kinpro1024/ErgoWarrior/Assets/ErgoWarrior_v0_alpha.jpg

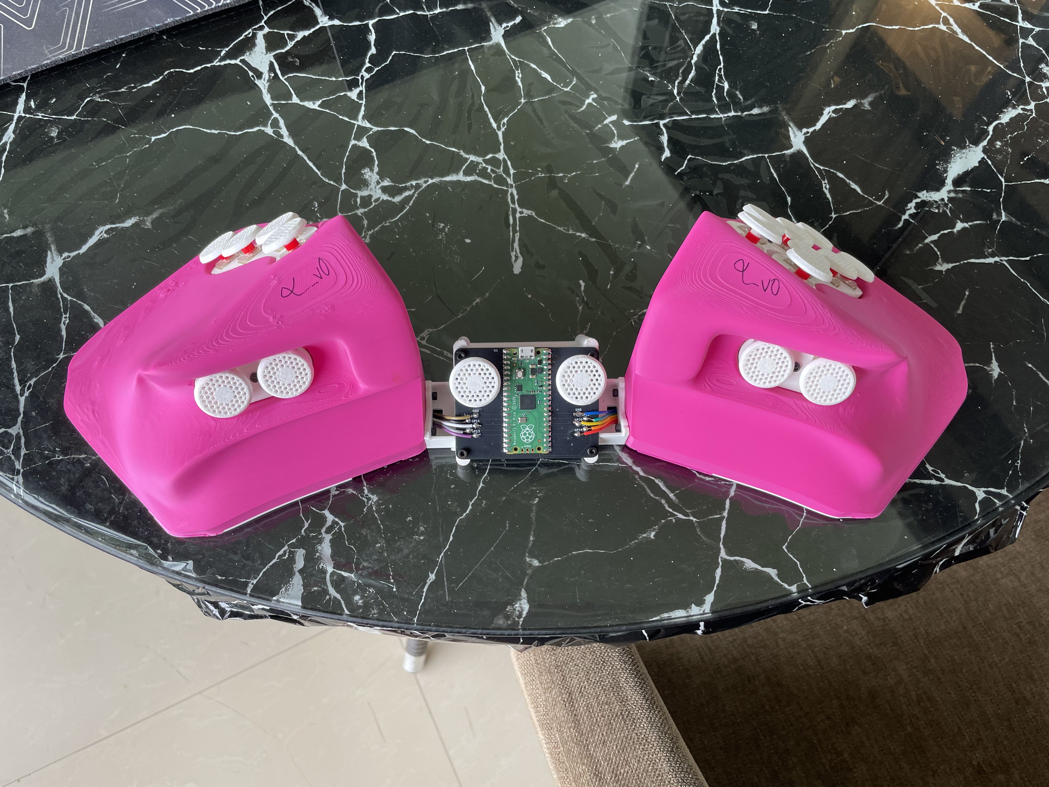
Assets/ErgoWarrior_v0_alpha.jpg
