kinpro1024/ErgoWarrior/Assets/Reference_Images/Screenshot 2025-11-22 at 19.15.04.png

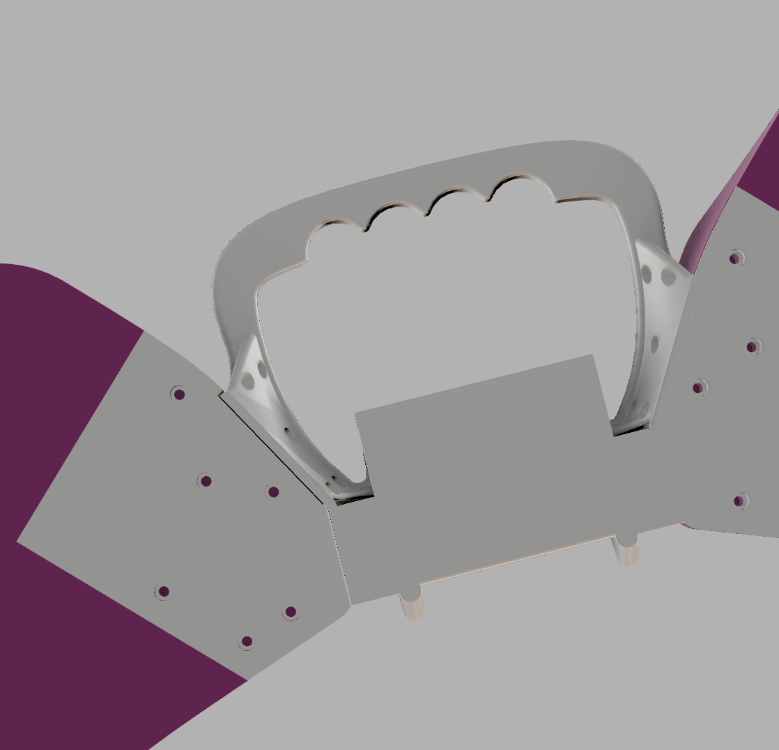
Assets/Reference_Images/Screenshot 2025-11-22 at 19.15.04.png
