kinpro1024/ErgoWarrior/Assets/Reference_Images/Screenshot 2025-11-22 at 19.16.22.png

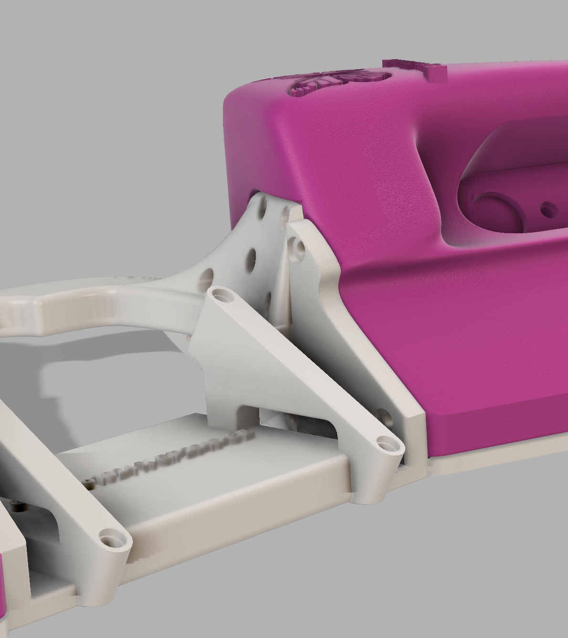
Assets/Reference_Images/Screenshot 2025-11-22 at 19.16.22.png
