kinpro1024/ErgoWarrior/Assets/v0_vs_v1_PCBs.jpg

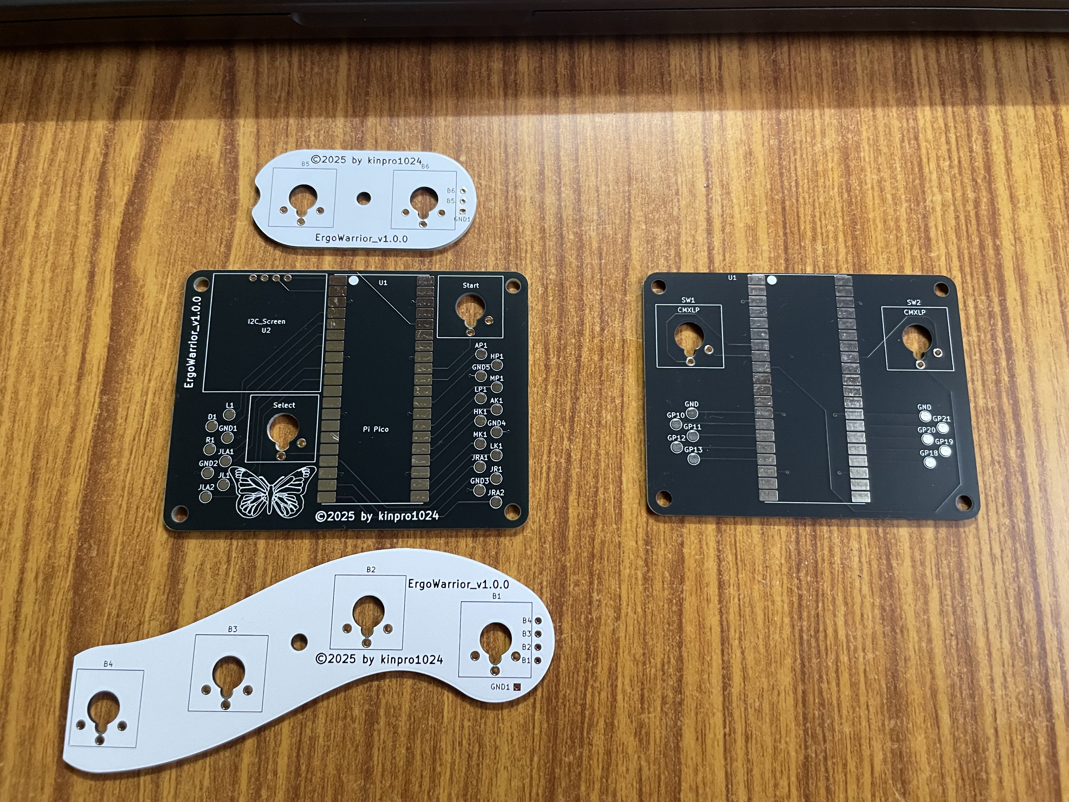
Assets/v0_vs_v1_PCBs.jpg
