kinpro1024/ErgoWarrior/Assets/WIP_Early_Right_Half.png

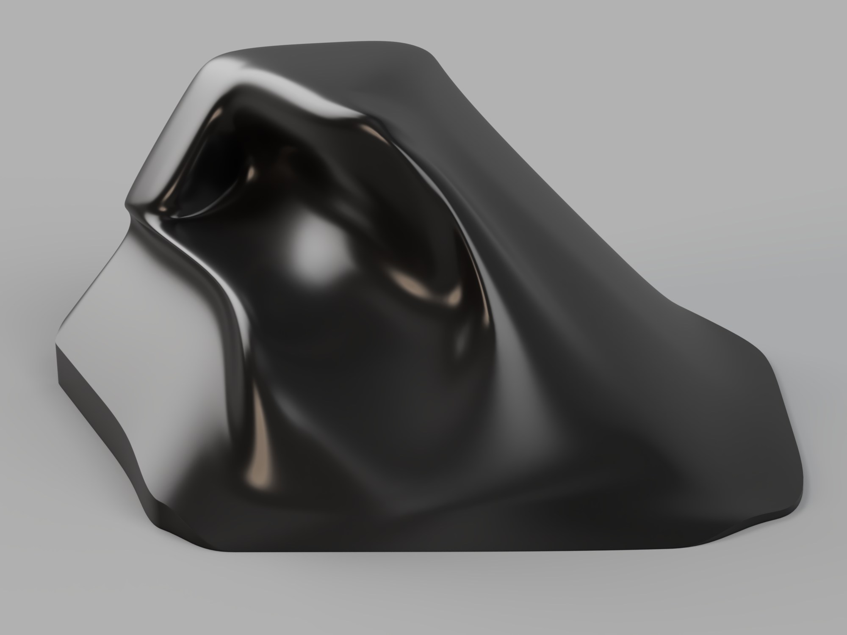
Assets/WIP_Early_Right_Half.png
