kinpro1024/ErgoWarrior/Assets/WIP_Right_Half.JPG

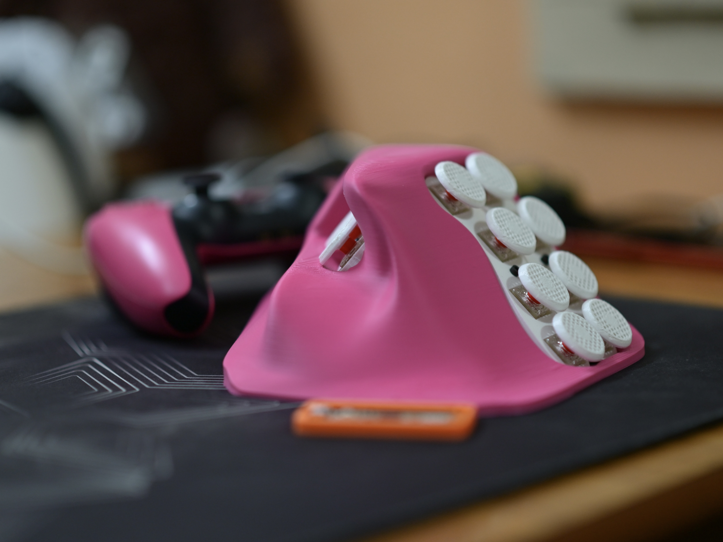
Assets/WIP_Right_Half.JPG
